frank26080115/bucket/elec/bucket-sch.png

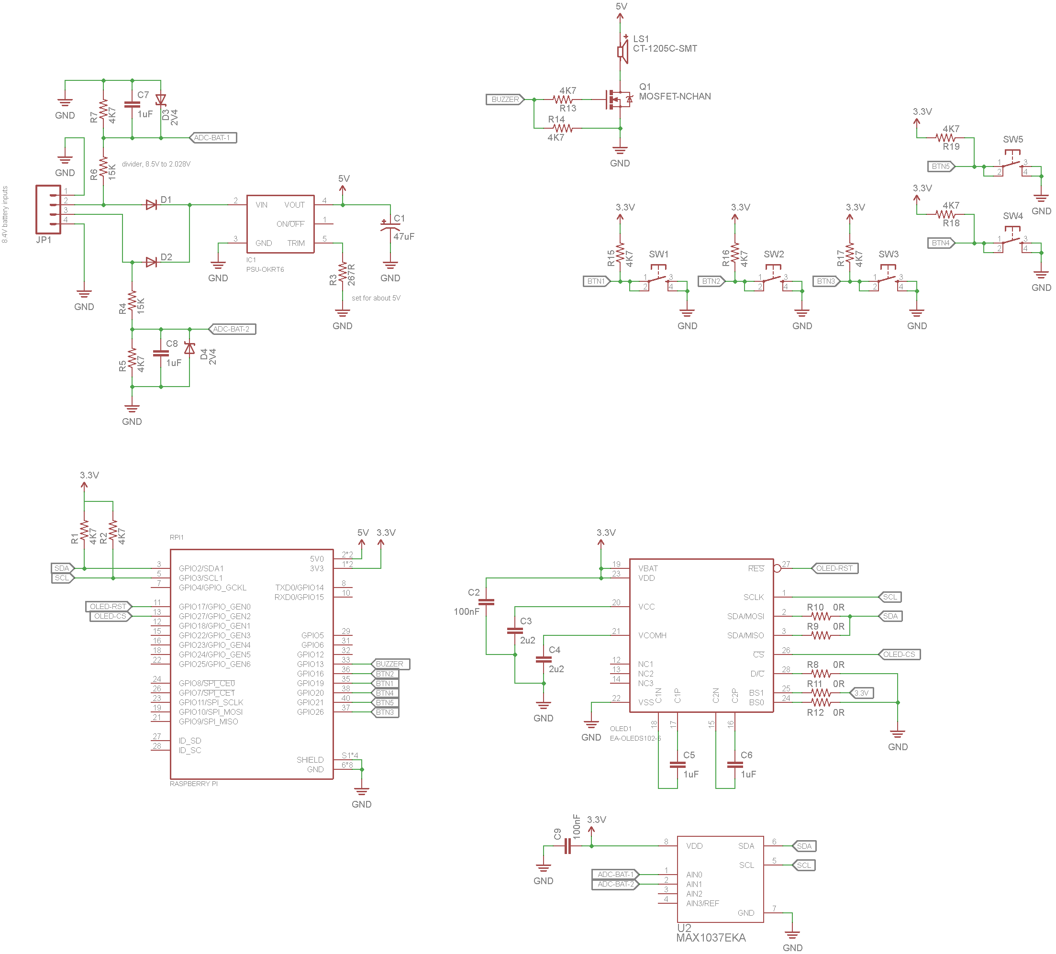
elec/bucket-sch.png
